elyoni/3d-keyboard-generator/Documents/2024-03-17_12-30.png

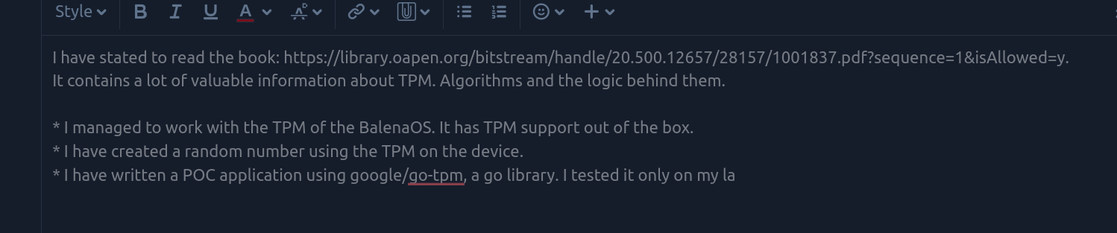
Documents/2024-03-17_12-30.png
